BoujeeEnjinia1701/fieldcell/cad/drawings/FCL-DWG-002.pdf

CONCEPT, NOT FOR FABRICATION | FieldCell · github.com/BoujeeEnjinia1701/fieldcell

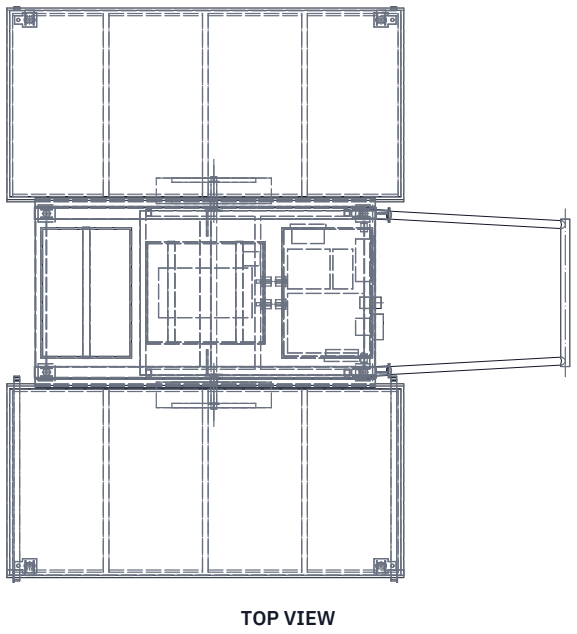
[picture p45: figure]
TOP VIEW

FRONT VIEW
Scale 1:25; looking at the front (along +Y)

Scale 1:25; looking down (along -Z)

RIGHT VIEW
Scale 1:25; looking at the right side (along -X)

1986

2030 916

460 deck

720 track

309

ISOMETRIC VIEW, STOWED FOR TRAVEL
Not to scale; seen from the front right and above, about 30 deg elevation

MAIN DIMENSIONS AND INTERFACES (MM)
Deployed 1,986 L x 2,030 W x 916 H; wingspan 2,012 Stowed, handle off: 1,400 x 830 x 1,220
Frame 1,200 x 600, 40 x 40 x 1.5 steel tube; deck 460 parked Wheels 406 dia., track 720; axle 30 toward handle
Hinge pin Y +/-330, Z 495; wings 15 deg below horizontal Hinge on 20 x 20 angle, welded tabs; wing to tyre 28
Sun shade on 4 uprights (item 18); tie bars (item 19)
Outlet face toward handle; grip at Z 900
Mass about 80.0 kg (FCL-CAL-001); 2 x 200 W PV, 1.28 kWh Third-angle; front view from -Y, right view from +X
REV | DESCRIPTION | DATE | BY
P1 | Preliminary GA for TRL 3 (from cad/src/model.py) | 2026-09-25 | AC
P2 | Hinge spacer +20 mm, sun shade added (DDR-002) | 2026-09-25 | AC
P3 | Layout and labels tidied | 2026-09-30 | AC
P4 | Constructable design (DDR-003): tabs, sockets, clevises, tie bars, shade uprights | 2026-10-01 | AC
FIELDCELL | github.com/BoujeeEnjinia1701/fieldcell

## General arrangement

DRAWING NO.
FCL-DWG-002

REV
P4

SHEET
1 of 1

SIZE

## ANSI B

SCALE
1:25

UNITS
mm
PROJECTION | DATE
2026-10-01

DRAWN
Amish Chadha

MATERIAL / NOTES
Welded steel frame, IP65 and IP54 enclosures; see bom/bom.csv. PRELIMINARY, NOT FOR FABRICATION
Licensed CERN-OHL-S-2.0 · Design Molecule Lab · designmolecule.com | Generated from cad/src; do not edit by hand
