BoujeeEnjinia1701/fieldcell/cad/drawings/FCL-DWG-101.pdf

### BUILD PLAN SKETCH, PLAN NOT YET BUILT FieldCell · github.com/BoujeeEnjinia1701/fieldcell

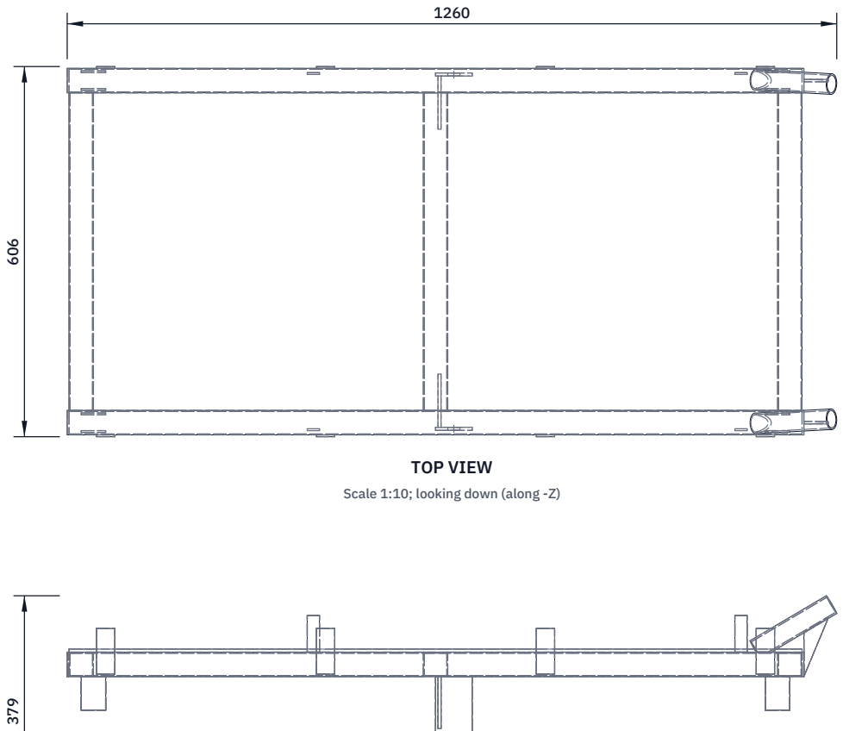
[picture p46: figure]
TOP VIEW; Scale 1:10; looking down (along -Z)
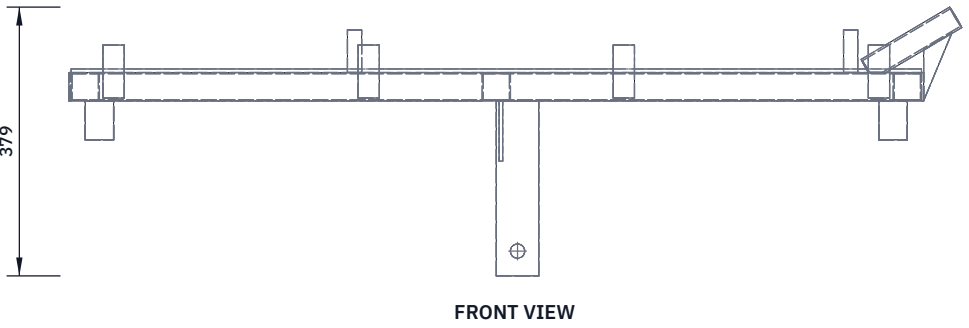
[picture p47: figure]
FRONT VIEW

Scale 1:10; looking at the front (along +Y)

RIGHT VIEW
Scale 1:10; looking at the right side (along -X)

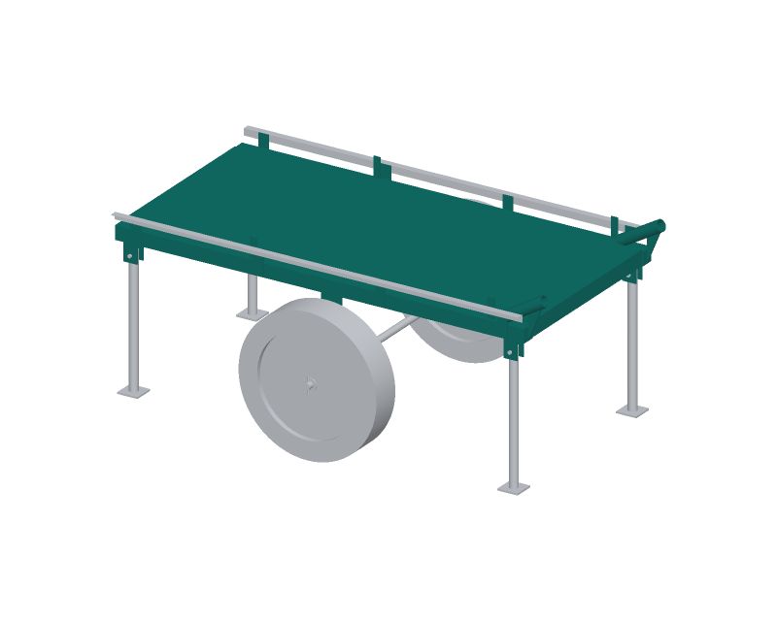
[picture p48: figure]

WHERE IT GOES
This part in colour, its neighbours in grey

HOW TO MAKE IT AND HOW IT FITS
Rails: two 1,200 mm lengths of 40 x 40 x 1.5 tube. Cross tubes: three
520 mm lengths, at both ends and the middle, between the rails.
Weld square on a flat table: diagonals equal within 2 mm. Tube tops
are 455 mm above the ground when parked. Cap the four rail ends (3 mm). Deck: expanded steel sheet 1,200 x 520 mm laid on the cross tubes between the rails, stitch welded 25 mm every 150 mm.
Axle brackets: 60 x 5 mm plate, 247 mm long, under each rail at 630 mm from the front end, 290 mm from the centre line; 20.5 mm axle hole
35 mm above the bottom. Gusset 87 x 85 x 5 mm to the middle cross tube. Hinge tabs: eight 30 x 3 mm, 75 mm long, on the rail outer faces at
60, 420, 780 and 1,140 mm from the front end, 39 mm above the rail top. Handle sockets, leg clevises, shade tabs: see the frame layout picture. Check: deck flat within 3 mm; axle holes line up (20 mm bar slides through).
REV | DESCRIPTION | DATE | BY
P1 | Making sketch for the prototype build plan | 2026-10-01 | AC
FIELDCELL | github.com/BoujeeEnjinia1701/fieldcell

## FieldCell frame weldment: making sketch

DRAWING NO.
FCL-DWG-101

REV
P1

SHEET
1 of 1

SIZE

## ANSI B

SCALE
1:10

UNITS
mm
PROJECTION | DATE
2026-10-01

DRAWN
Amish Chadha

MATERIAL / NOTES
Steel square tube 40 x 40 x 1.5, S235; expanded steel sheet; 3 to 5 mm plate
Licensed CERN-OHL-S-2.0 · Design Molecule Lab · designmolecule.com | Generated from cad/src; do not edit by hand
