BoujeeEnjinia1701/fieldcell/cad/drawings/FCL-DWG-102.pdf

### BUILD PLAN SKETCH, PLAN NOT YET BUILT FieldCell · github.com/BoujeeEnjinia1701/fieldcell

FRONT VIEW
Scale 1:5; looking at the front (along +Y)

TOP VIEW
Scale 1:5; looking down (along -Z)

RIGHT VIEW
Scale 1:5; looking at the right side (along -X)

820

20 20

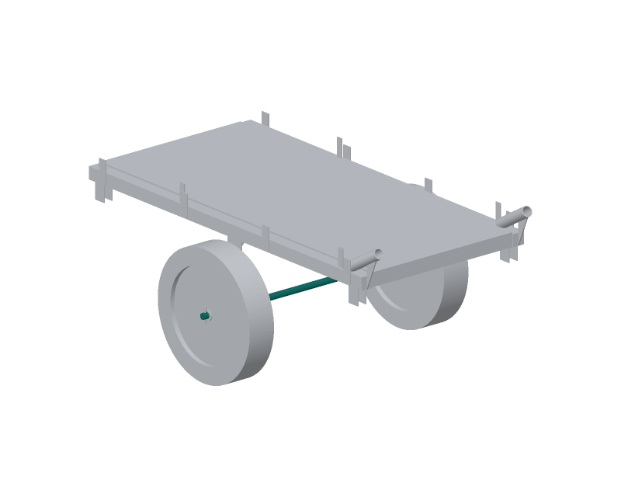
[picture p49: figure]

WHERE IT GOES
This part in colour, its neighbours in grey

HOW TO MAKE IT AND HOW IT FITS
Cut 820 mm of 20 mm bright steel bar; chamfer both ends 1 mm. Drill a 5 mm cross hole 10 mm from each end for the linch pins, both holes in the same plane.
Slide it through both bracket holes so 410 mm stands each side of the centre line; weld it to both brackets, all round, both faces. Each end then takes, in order: a spacer collar 26 mm outside,
20 mm bore, 37.5 mm long; the wheel hub (60 mm long);
a 20 mm washer 3 mm thick; the linch pin.
Check: the wheels spin freely with 0.5 to 1 mm end float.
REV | DESCRIPTION | DATE | BY
P1 | Making sketch for the prototype build plan | 2026-10-01 | AC
FIELDCELL | github.com/BoujeeEnjinia1701/fieldcell

## FieldCell axle: making sketch

DRAWING NO.
FCL-DWG-102

REV
P1

SHEET
1 of 1

SIZE

## ANSI B

SCALE
1:5

UNITS
mm
PROJECTION | DATE
2026-10-01

DRAWN
Amish Chadha

MATERIAL / NOTES
Bright mild steel bar 20 mm diameter
Licensed CERN-OHL-S-2.0 · Design Molecule Lab · designmolecule.com | Generated from cad/src; do not edit by hand
