BoujeeEnjinia1701/fieldcell/cad/drawings/FCL-DWG-103.pdf

### BUILD PLAN SKETCH, PLAN NOT YET BUILT FieldCell · github.com/BoujeeEnjinia1701/fieldcell

FRONT VIEW
Scale 1:5; looking at the front (along +Y)

TOP VIEW
Scale 1:5; looking down (along -Z)

RIGHT VIEW
Scale 1:5; looking at the right side (along -X)

60

60 392

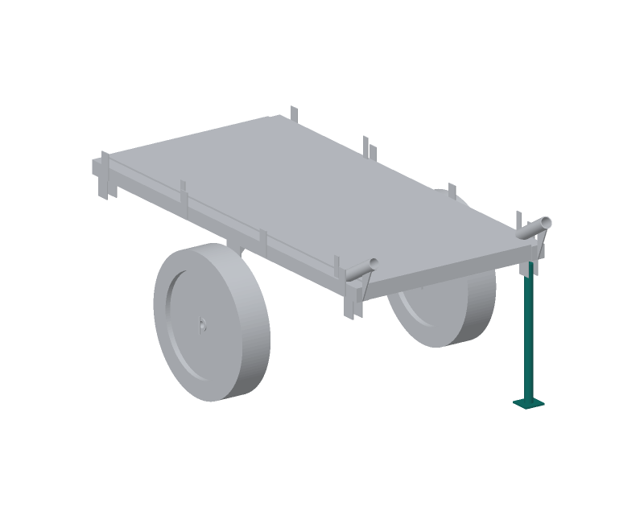
[picture p50: figure]

WHERE IT GOES
This part in colour, its neighbours in grey

HOW TO MAKE IT AND HOW IT FITS
Cut four 387 mm lengths of 25 x 2 mm tube; round the top end. Drill 10.5 mm across the tube 12 mm from the top: the pivot. Drill 6.5 mm across, 30 mm below the pivot hole: the detent hole that locks the leg down.
Weld a 60 x 60 x 5 mm foot plate square on the bottom end. Fit: the top end goes between a pair of 3 mm clevis plates under the rail, 40 mm from the rail end; M10 pivot bolt, nyloc nut, snug so the leg swings. Spring detent pin through the clevis and the leg holds it down; a second clevis hole holds it folded. The leg folds inward along the rail, foot toward the axle. Check: with all four down the deck is level within 1 degree.
REV | DESCRIPTION | DATE | BY
P1 | Making sketch for the prototype build plan | 2026-10-01 | AC
FIELDCELL | github.com/BoujeeEnjinia1701/fieldcell

## FieldCell stand leg (make 4): making sketch

DRAWING NO.
FCL-DWG-103

REV
P1

SHEET
1 of 1

SIZE

## ANSI B

SCALE
1:5

UNITS
mm
PROJECTION | DATE
2026-10-01

DRAWN
Amish Chadha

MATERIAL / NOTES
Steel tube 25 x 2 mm; steel plate 5 mm
Licensed CERN-OHL-S-2.0 · Design Molecule Lab · designmolecule.com | Generated from cad/src; do not edit by hand
