BoujeeEnjinia1701/fieldcell/cad/drawings/FCL-DWG-104.pdf

### BUILD PLAN SKETCH, PLAN NOT YET BUILT FieldCell · github.com/BoujeeEnjinia1701/fieldcell

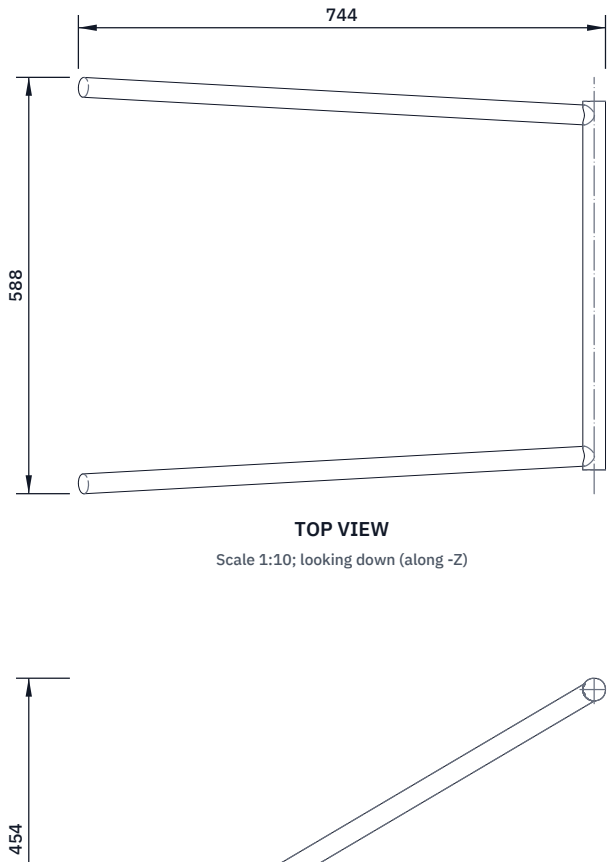
[picture p51: figure]
TOP VIEW; Scale 1:10; looking down (along -Z)

FRONT VIEW
Scale 1:10; looking at the front (along +Y)

RIGHT VIEW
Scale 1:10; looking at the right side (along -X)

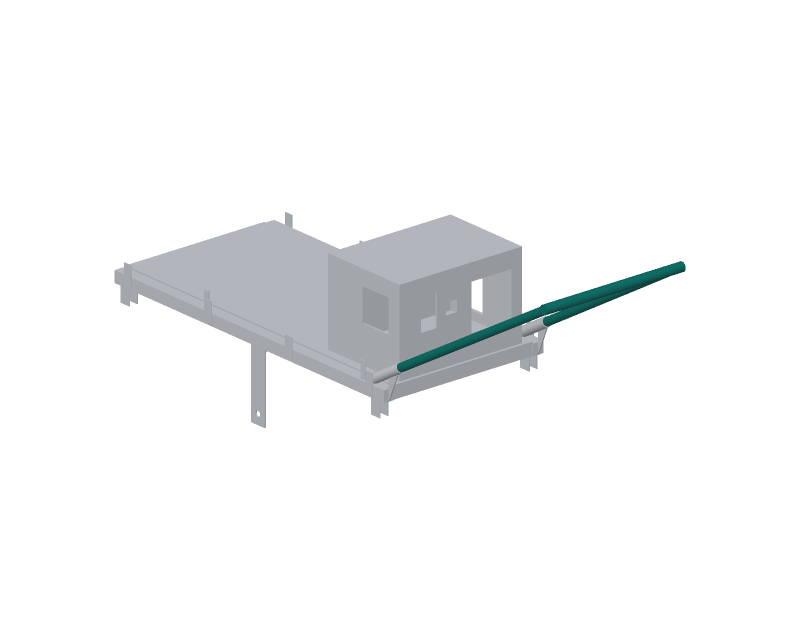
[picture p52: figure]

WHERE IT GOES
This part in colour, its neighbours in grey

HOW TO MAKE IT AND HOW IT FITS
Legs: two 843 mm lengths of 28 x 1.5 mm tube.
Grip: 520 mm of 32 x 1.5 mm tube.
Lay out on the bench: leg feet 560 mm apart, leg tops 480 mm apart, meeting the grip 20 mm in from each grip end. Fish-mouth the leg tops to the grip and weld.
Each leg drops into a socket on the rail end, 30.5 degrees up from level; mark the leg 115 mm from its foot and drill 8.5 mm across it with the leg in the socket, through the socket's pin hole. Quick-release pins hold the handle; pull them to take it off.
Grip 900 mm above the ground, 1,270 mm from the deck centre. Check: the handle drops in and out of both sockets without forcing.
REV | DESCRIPTION | DATE | BY
P1 | Making sketch for the prototype build plan | 2026-10-01 | AC
FIELDCELL | github.com/BoujeeEnjinia1701/fieldcell

## FieldCell handle: making sketch

DRAWING NO.
FCL-DWG-104

REV
P1

SHEET
1 of 1

SIZE

## ANSI B

SCALE
1:10

UNITS
mm
PROJECTION | DATE
2026-10-01

DRAWN
Amish Chadha

MATERIAL / NOTES
Steel tube 28 x 1.5 mm (legs), 32 x 1.5 mm (grip)
Licensed CERN-OHL-S-2.0 · Design Molecule Lab · designmolecule.com | Generated from cad/src; do not edit by hand
