BoujeeEnjinia1701/fieldcell/cad/drawings/FCL-DWG-105.pdf

### BUILD PLAN SKETCH, PLAN NOT YET BUILT FieldCell · github.com/BoujeeEnjinia1701/fieldcell

FRONT VIEW
Scale 1:10; looking at the front (along +Y)

TOP VIEW
Scale 1:10; looking down (along -Z)

RIGHT VIEW
Scale 1:10; looking at the right side (along -X)

1200

20 20

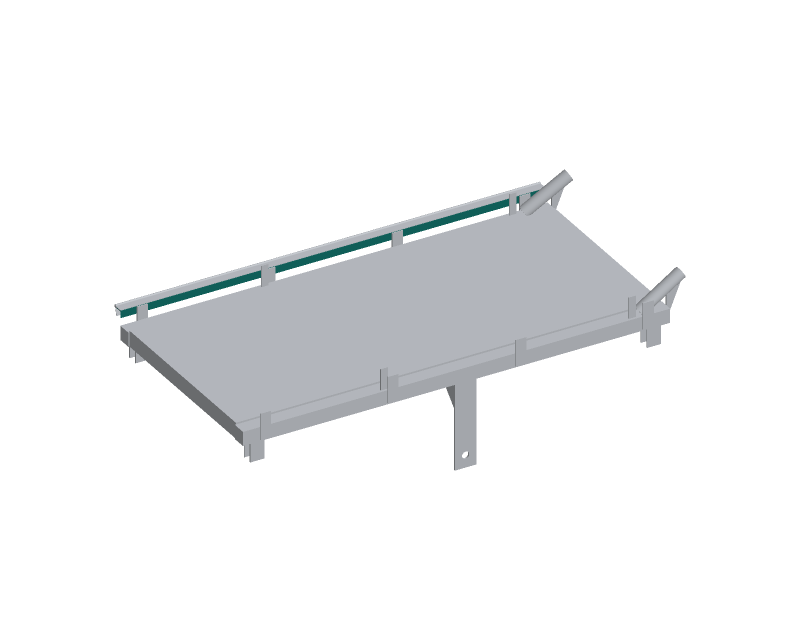
[picture p53: figure]

WHERE IT GOES
This part in colour, its neighbours in grey

HOW TO MAKE IT AND HOW IT FITS
Cut two 1,200 mm lengths of 20 x 20 x 2 mm angle; deburr. Upright leg: four 5.5 mm holes 11 mm down from the top, at 60, 420, 780 and 1,140 mm from one end, to match the frame tabs. Flat leg (top): 4.5 mm holes every 150 mm, 10 mm in from the outer edge, for the hinge screws; countersink from the top. Fit: upright leg flat on the outside of the four tabs, top of the flat leg 494 mm above the ground, flat leg pointing outward. M5 bolts through the tabs, nyloc nuts inside.
The hinge's fixed leaf lies on the flat leg; its knuckle (the pin) overhangs the angle's edge by 7 mm.
Check: angle top level and straight within 1 mm along its length.
REV | DESCRIPTION | DATE | BY
P1 | Making sketch for the prototype build plan | 2026-10-01 | AC
FIELDCELL | github.com/BoujeeEnjinia1701/fieldcell

## FieldCell hinge spacer angle (make 2): making sketch

DRAWING NO.
FCL-DWG-105

REV
P1

SHEET
1 of 1

SIZE

## ANSI B

SCALE
1:10

UNITS
mm
PROJECTION | DATE
2026-10-01

DRAWN
Amish Chadha

MATERIAL / NOTES
Aluminium equal angle 20 x 20 x 2 mm, 6063
Licensed CERN-OHL-S-2.0 · Design Molecule Lab · designmolecule.com | Generated from cad/src; do not edit by hand
