BoujeeEnjinia1701/fieldcell/cad/drawings/FCL-DWG-106.pdf

### BUILD PLAN SKETCH, PLAN NOT YET BUILT FieldCell · github.com/BoujeeEnjinia1701/fieldcell

FRONT VIEW
Scale 1:10; looking at the front (along +Y)

TOP VIEW
Scale 1:10; looking down (along -Z)

RIGHT VIEW
Scale 1:10; looking at the right side (along -X)

1400

700 30

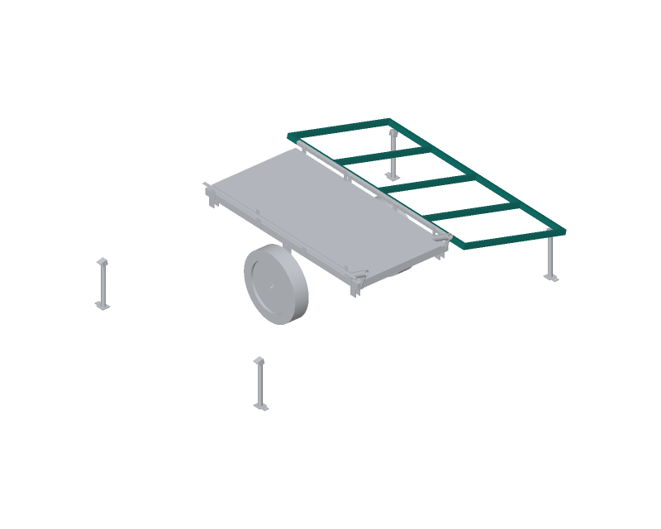
[picture p54: figure]

WHERE IT GOES
This part in colour, its neighbours in grey

HOW TO MAKE IT AND HOW IT FITS
Long members: two 1,400 mm lengths. End members and ribs: five
660 mm lengths. All 30 x 20 x 1.5 tube, 30 mm side upright.
Ribs at 350, 700 and 1,050 mm from one end, square to the long members. Join every butt with an aluminium corner cleat inside the tubes and
four 4.8 mm blind rivets (or TIG weld). Frame 1,400 x 700 mm.
Face (top): flat within 2 mm; the module is bonded to it.
Inner long member (hinge side): M4 rivet nuts every 150 mm in its inner face, 10 mm below the top, for the hinge's moving leaf.
Outer long member: outrigger brackets underneath at 80 mm from each end; tie bar bracket (left wing) or keeper (right wing) at each end. Check: diagonals equal within 2 mm; frame does not rock on a table.
REV | DESCRIPTION | DATE | BY
P1 | Making sketch for the prototype build plan | 2026-10-01 | AC
FIELDCELL | github.com/BoujeeEnjinia1701/fieldcell

## FieldCell PV wing frame (make 2): making sketch

DRAWING NO.
FCL-DWG-106

REV
P1

SHEET
1 of 1

SIZE

## ANSI B

SCALE
1:10

UNITS
mm
PROJECTION | DATE
2026-10-01

DRAWN
Amish Chadha

MATERIAL / NOTES
Aluminium rectangular tube 30 x 20 x 1.5 mm, 6063
Licensed CERN-OHL-S-2.0 · Design Molecule Lab · designmolecule.com | Generated from cad/src; do not edit by hand
