BoujeeEnjinia1701/fieldcell/cad/drawings/FCL-DWG-107.pdf

### BUILD PLAN SKETCH, PLAN NOT YET BUILT FieldCell · github.com/BoujeeEnjinia1701/fieldcell

FRONT VIEW
Scale 1:5; looking at the front (along +Y)

TOP VIEW
Scale 1:5; looking down (along -Z)

RIGHT VIEW
Scale 1:5; looking at the right side (along -X)

78

50 273

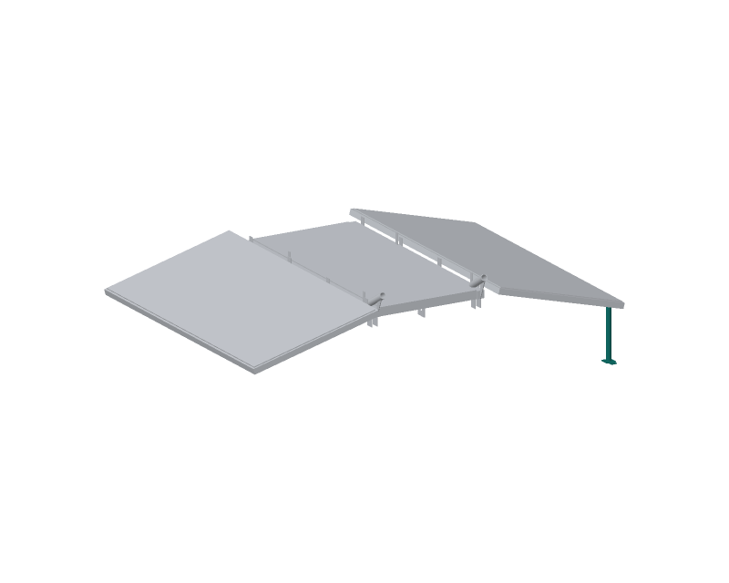
[picture p55: figure]

WHERE IT GOES
This part in colour, its neighbours in grey

HOW TO MAKE IT AND HOW IT FITS
Leg: cut 269 mm of 25 x 2 mm tube; round the top end; drill 8.5 mm across, 10 mm from the top (pivot), and 6.5 mm 30 mm below it (detent). Foot: 50 x 50 x 4 mm plate with a 28 x 30 mm stake tab on one side
(11 mm hole, 15 mm from the plate edge); weld square to the leg.
The tab points toward the nearer end of the cart.
Bracket: bend a 3 mm aluminium strip into a U, 26 mm inside, legs 29 mm, web 45 mm long; 8.5 mm pivot hole through both legs. Fit: rivet the web under the wing's outer long member, 80 mm from the frame end; M8 pivot bolt, nyloc nut, snug.
Leg down: vertical with the wing at 15 degrees. Folded: flat under the wing, 7 mm clear of the frame.
Check: the wing's outer edge sits 309 mm above the ground.
REV | DESCRIPTION | DATE | BY
P1 | Making sketch for the prototype build plan | 2026-10-01 | AC
FIELDCELL | github.com/BoujeeEnjinia1701/fieldcell

## FieldCell outrigger leg and bracket (make 4): making sketch

DRAWING NO.
FCL-DWG-107

REV
P1

SHEET
1 of 1

SIZE

## ANSI B

SCALE
1:5

UNITS
mm
PROJECTION | DATE
2026-10-01

DRAWN
Amish Chadha

MATERIAL / NOTES
Steel tube 25 x 2 mm, steel plate 4 mm; aluminium strip 3 mm (bracket)
Licensed CERN-OHL-S-2.0 · Design Molecule Lab · designmolecule.com | Generated from cad/src; do not edit by hand
