BoujeeEnjinia1701/fieldcell/cad/drawings/FCL-DWG-108.pdf

### BUILD PLAN SKETCH, PLAN NOT YET BUILT FieldCell · github.com/BoujeeEnjinia1701/fieldcell

FRONT VIEW
Scale 1:5; looking at the front (along +Y)

TOP VIEW
Scale 1:5; looking down (along -Z)

RIGHT VIEW
Scale 1:5; looking at the right side (along -X)

743

20 20

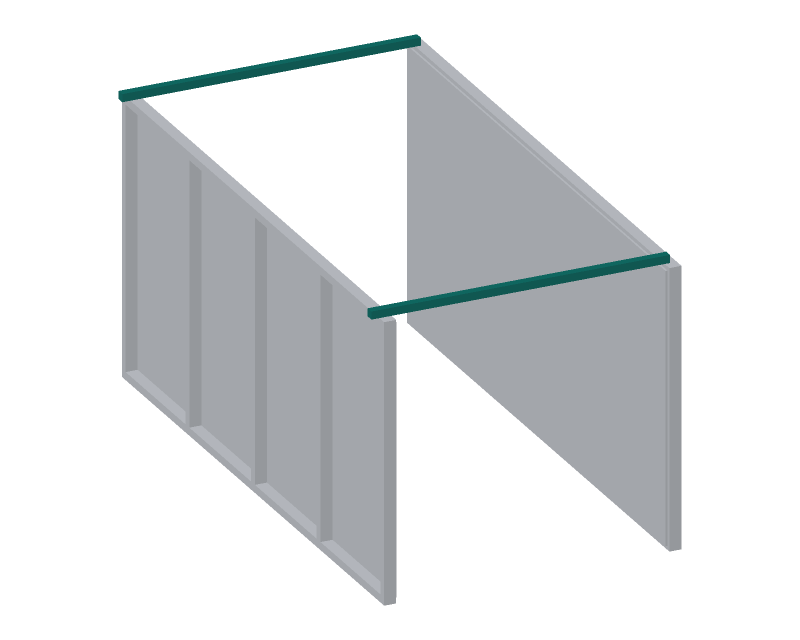
[picture p56: figure]

WHERE IT GOES
This part in colour, its neighbours in grey

HOW TO MAKE IT AND HOW IT FITS
Cut two 731 mm lengths of 20 x 20 x 1.5 mm square tube; deburr (743 mm overall with the latch body on the end).
Drill 6.5 mm across, 10 mm from one end: the pivot.
Rivet the over-centre latch body to the other end, hook outward. Pivot bracket: 3 mm aluminium angle, ear 35 mm tall beside the bar, riveted to the top corner of the left wing's frame, on its back. Keeper: screwed to the top of the right wing's outer member,
12 mm in from its back face, opposite the latch.
Travel: the bar lies across the tops of both stowed wings and the latch pulls the right wing in against it.
Parked: the bar folds down the back of the left wing, held by a clip. Check: latched, neither wing moves when pushed outward at the top.
REV | DESCRIPTION | DATE | BY
P1 | Making sketch for the prototype build plan | 2026-10-01 | AC
FIELDCELL | github.com/BoujeeEnjinia1701/fieldcell

## FieldCell tie bar (make 2): making sketch

DRAWING NO.
FCL-DWG-108

REV
P1

SHEET
1 of 1

SIZE

## ANSI B

SCALE
1:5

UNITS
mm
PROJECTION | DATE
2026-10-01

DRAWN
Amish Chadha

MATERIAL / NOTES
Aluminium square tube 20 x 20 x 1.5 mm, 6063
Licensed CERN-OHL-S-2.0 · Design Molecule Lab · designmolecule.com | Generated from cad/src; do not edit by hand
