BoujeeEnjinia1701/fieldcell/cad/drawings/FCL-DWG-109.pdf

### BUILD PLAN SKETCH, PLAN NOT YET BUILT FieldCell · github.com/BoujeeEnjinia1701/fieldcell

FRONT VIEW
Scale 1:10; looking at the front (along +Y)

TOP VIEW
Scale 1:10; looking down (along -Z)

RIGHT VIEW
Scale 1:10; looking at the right side (along -X)

830

580 375

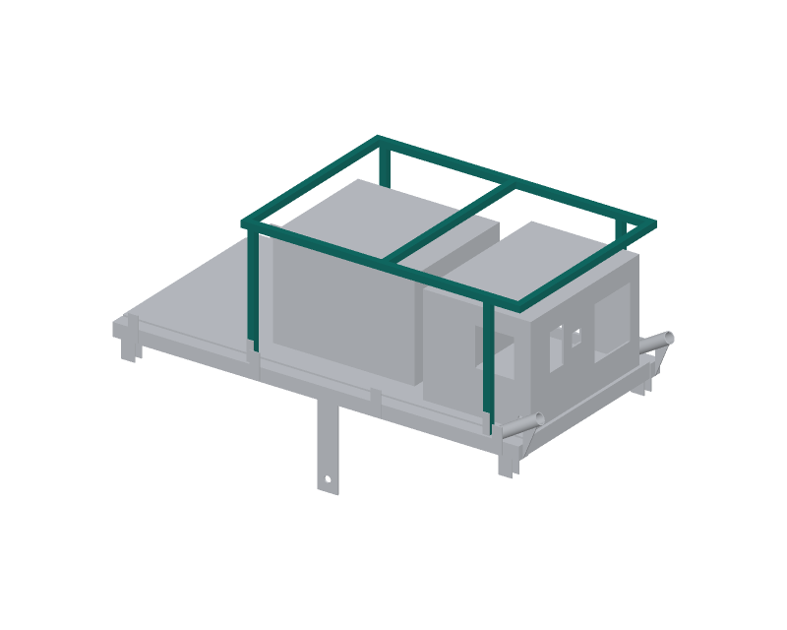
[picture p57: figure]

WHERE IT GOES
This part in colour, its neighbours in grey

HOW TO MAKE IT AND HOW IT FITS
Frame: two 830 mm long sides, three 540 mm cross tubes (ends and middle), 20 x 20 x 1.5 mm; corner cleats and rivets. 830 x 580 mm. Fabric: reflective aluminized fabric, 830 x 580 mm, eyelets every 100 mm, laced round the frame, shiny side up.
Uprights: four 355 mm lengths of the same tube. 6.5 mm hole across each, 30 mm from the bottom, for the M6 bolt into the frame tab. Uprights stand on the rail tops at 400 and 1,100 mm from the front end, 280 mm each side of the centre line.
The frame's long sides rest on the upright tops 810 mm above the ground, 50 mm over both boxes; an angle clip and M6 wing bolt at each upright. Undo four wing bolts to lift the shade off and open the battery lid.
Check: 50 mm air gap over both boxes; shade level within 5 mm.
REV | DESCRIPTION | DATE | BY
P1 | Making sketch for the prototype build plan | 2026-10-01 | AC
FIELDCELL | github.com/BoujeeEnjinia1701/fieldcell

## FieldCell sun shade frame and uprights: making sketch

DRAWING NO.
FCL-DWG-109

REV
P1

SHEET
1 of 1

SIZE

## ANSI B

SCALE
1:10

UNITS
mm
PROJECTION | DATE
2026-10-01

DRAWN
Amish Chadha

MATERIAL / NOTES
Aluminium square tube 20 x 20 x 1.5 mm; aluminized fabric
Licensed CERN-OHL-S-2.0 · Design Molecule Lab · designmolecule.com | Generated from cad/src; do not edit by hand
