BoujeeEnjinia1701/fieldcell/cad/drawings/FCL-DWG-110.pdf

### BUILD PLAN SKETCH, PLAN NOT YET BUILT FieldCell · github.com/BoujeeEnjinia1701/fieldcell

FRONT VIEW
Scale 1:10; looking at the front (along +Y)

TOP VIEW
Scale 1:10; looking down (along -Z)

RIGHT VIEW
Scale 1:10; looking at the right side (along -X)

320

460 260

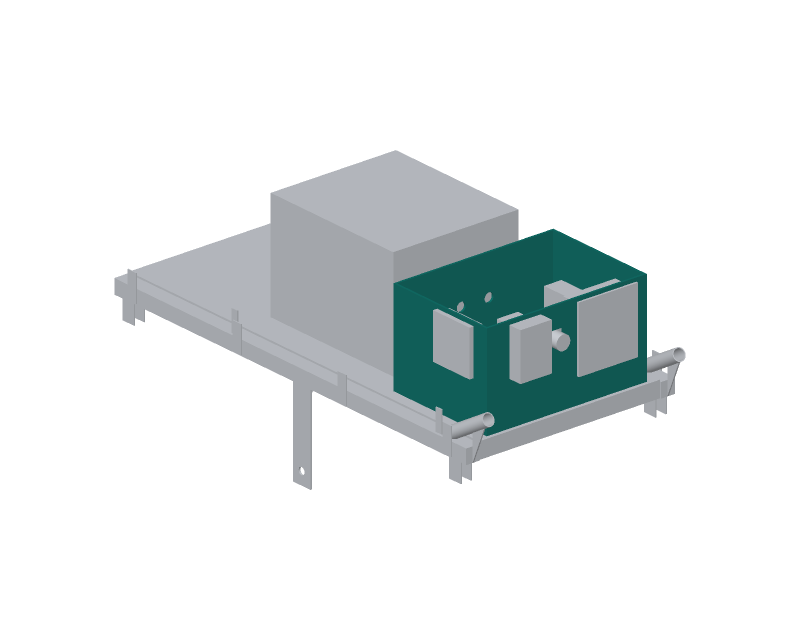
[picture p58: figure]

WHERE IT GOES
This part in colour, its neighbours in grey

HOW TO MAKE IT AND HOW IT FITS
Sizes are from the box's outside bottom edge and its centre line. Outlet end (toward the handle): DC panel 150 x 160 mm, 40 to 190 mm right of centre, 80 to 240 mm up; AC outlet 60 x 110 mm, 90 to 150 mm left, 130 to 240 mm up; isolator 40 x 40 mm, 15 to 55 mm left, 160 to 200 mm up. (Right and left as seen facing that end.)
Right side wall: fan 115 x 115 mm, 35 to 150 mm from the battery end, 35 to 150 mm up. Left wall: exhaust 115 x 115 mm, 155 to 270 mm from the battery end, 130 to 245 mm up.
Battery end: two 25.5 mm gland holes, 40 mm each side, 150 mm up. Both side walls: a 16.5 mm PV gland hole 30 mm from the outlet end, 30 mm up. Floor: four 6.5 mm holes for the deck bolts.
Cut with a step drill and a fine jigsaw; tape first; no solvents.
REV | DESCRIPTION | DATE | BY
P1 | Making sketch for the prototype build plan | 2026-10-01 | AC
FIELDCELL | github.com/BoujeeEnjinia1701/fieldcell

## FieldCell electronics box: cutting sketch

DRAWING NO.
FCL-DWG-110

REV
P1

SHEET
1 of 1

SIZE

## ANSI B

SCALE
1:10

UNITS
mm
PROJECTION | DATE
2026-10-01

DRAWN
Amish Chadha

MATERIAL / NOTES
Bought IP54 polycarbonate box 320 x 460 x 300 mm
Licensed CERN-OHL-S-2.0 · Design Molecule Lab · designmolecule.com | Generated from cad/src; do not edit by hand
