BoujeeEnjinia1701/fieldcell/cad/drawings/FCL-DWG-111.pdf

### BUILD PLAN SKETCH, PLAN NOT YET BUILT FieldCell · github.com/BoujeeEnjinia1701/fieldcell

FRONT VIEW
Scale 1:5; looking at the front (along +Y)

TOP VIEW
Scale 1:5; looking down (along -Z)

RIGHT VIEW
Scale 1:5; looking at the right side (along -X)

420

360 260

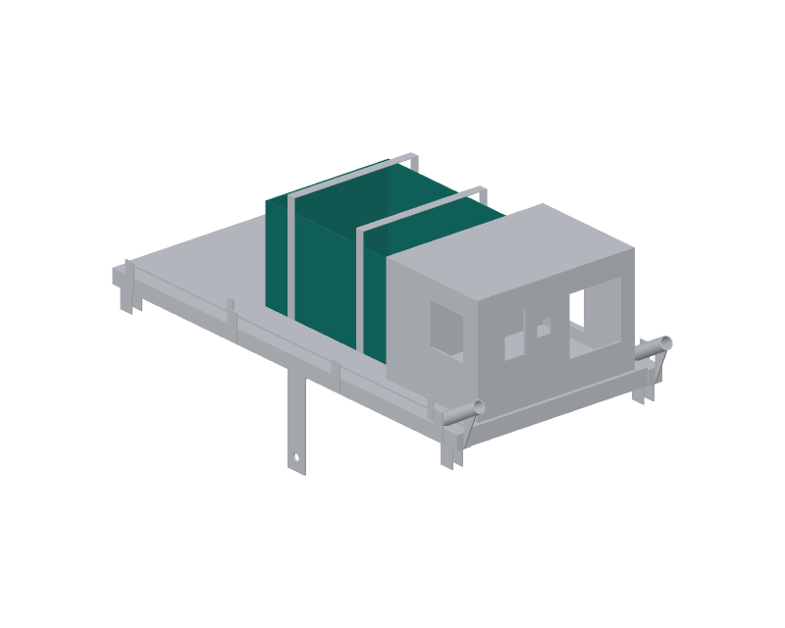
[picture p59: figure]

WHERE IT GOES
This part in colour, its neighbours in grey

HOW TO MAKE IT AND HOW IT FITS
Only the end facing the electronics box is drilled.
Two 25.5 mm holes for M25 glands, 40 mm each side of the centre line, 150 mm up from the outside bottom: they line up with the gland holes in the electronics box, 60 mm away.
Tape, pilot 3 mm, open with a step drill; deburr; no solvents.
Keep the case's own pressure vent; do not block it.
Inside: the pack sits in the middle of the floor on a 3 mm rubber mat with foam blocks round it; the class T fuse holder is screwed to
the floor beside the pack at the gland end, so the positive lead
from the pack to the fuse is under 150 mm.
Two cam straps hold the case and lid down through the deck. Check: glands seat flat; lid closes on its seal with the cables in.
REV | DESCRIPTION | DATE | BY
P1 | Making sketch for the prototype build plan | 2026-10-01 | AC
FIELDCELL | github.com/BoujeeEnjinia1701/fieldcell

## FieldCell battery case: drilling sketch

DRAWING NO.
FCL-DWG-111

REV
P1

SHEET
1 of 1

SIZE

## ANSI B

SCALE
1:5

UNITS
mm
PROJECTION | DATE
2026-10-01

DRAWN
Amish Chadha

MATERIAL / NOTES
Bought IP65 polypropylene case about 420 x 360 x 300 mm
Licensed CERN-OHL-S-2.0 · Design Molecule Lab · designmolecule.com | Generated from cad/src; do not edit by hand
