BoujeeEnjinia1701/fieldcell/cad/drawings/FCL-DWG-002.png

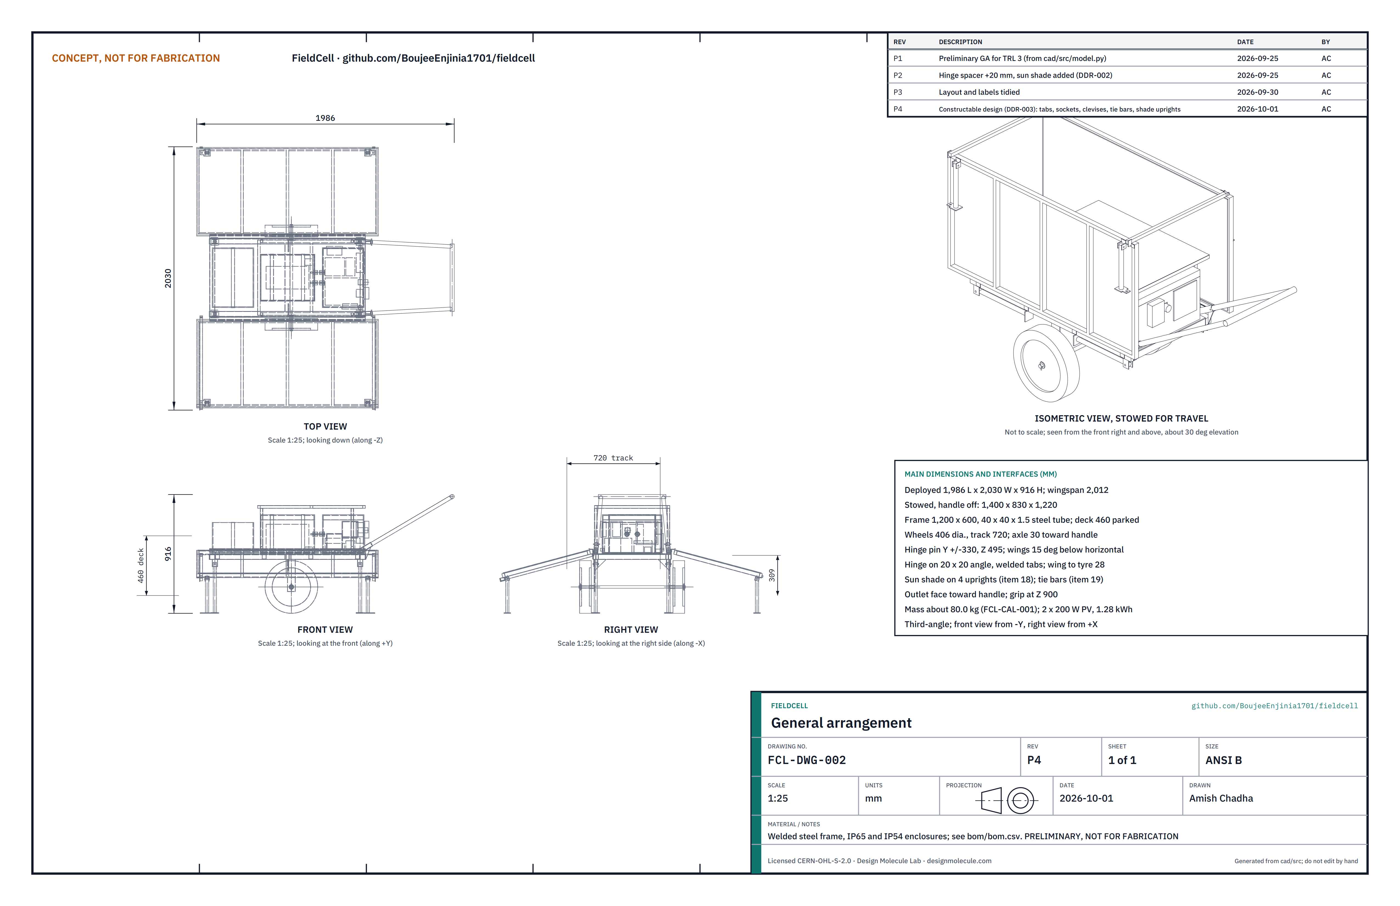
cad/drawings/FCL-DWG-002.png
