BoujeeEnjinia1701/fieldcell/media/card.png

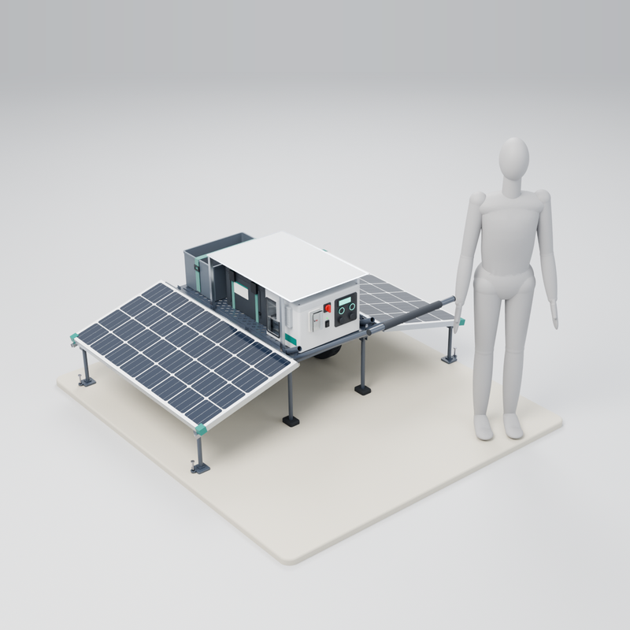
media/card.png
