BoujeeEnjinia1701/fieldcell/media/concept-blueprint.png

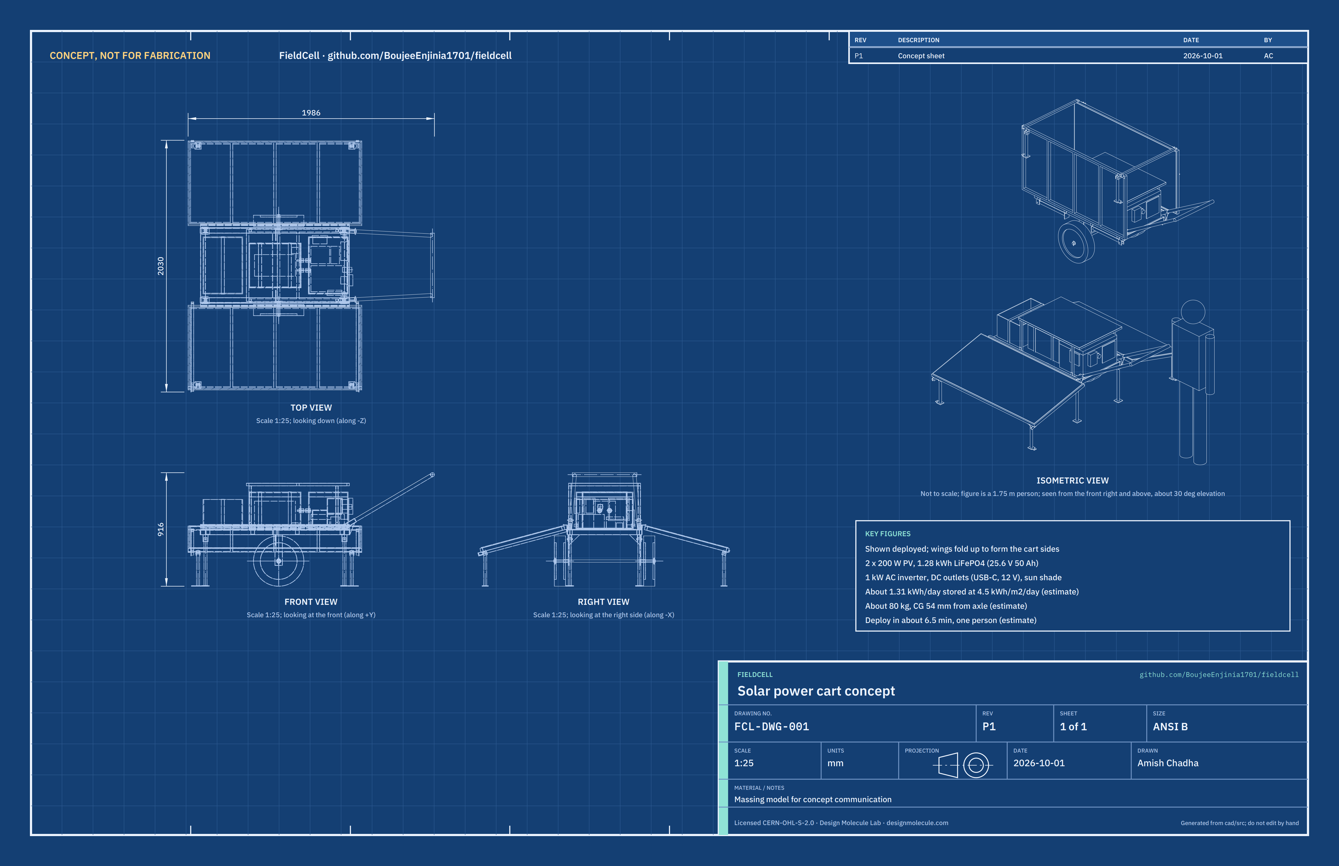
media/concept-blueprint.png
