BoujeeEnjinia1701/fieldcell/media/cutaway.png

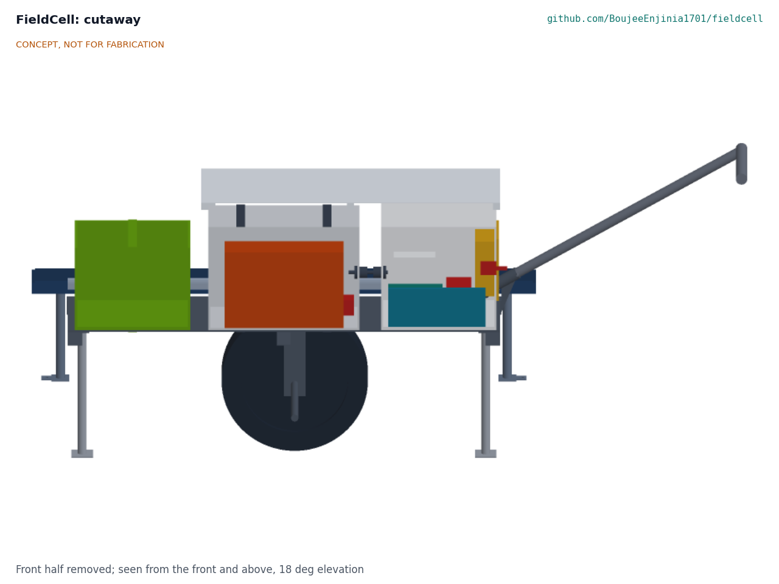
media/cutaway.png
