BoujeeEnjinia1701/fieldcell/media/render-detail.png

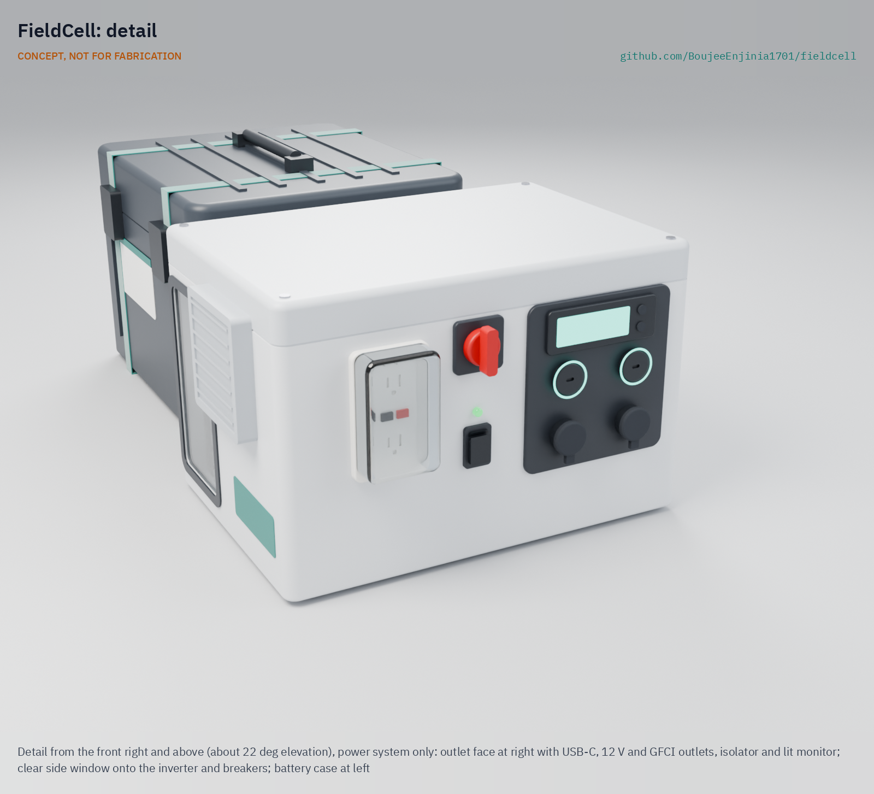
media/render-detail.png
