BoujeeEnjinia1701/fieldcell/media/render-exploded.png

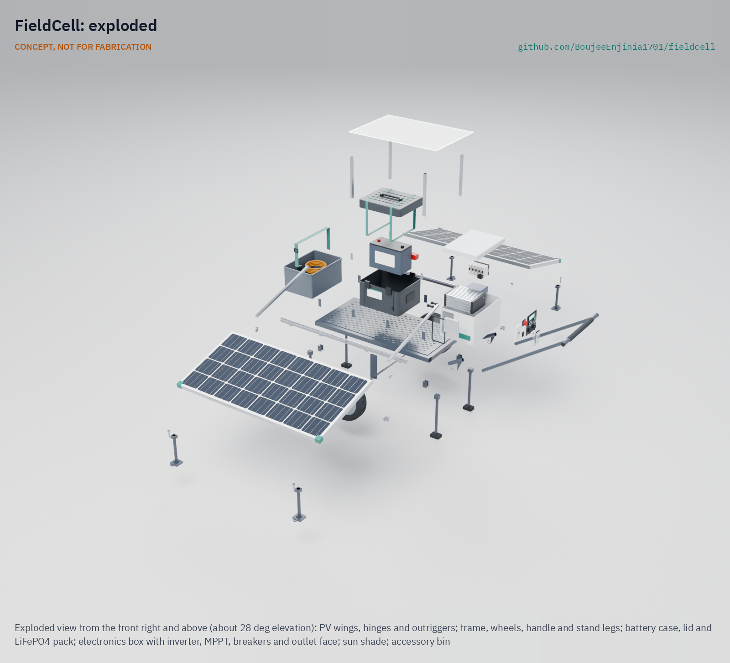
media/render-exploded.png
