BoujeeEnjinia1701/fieldcell/media/social-preview.png

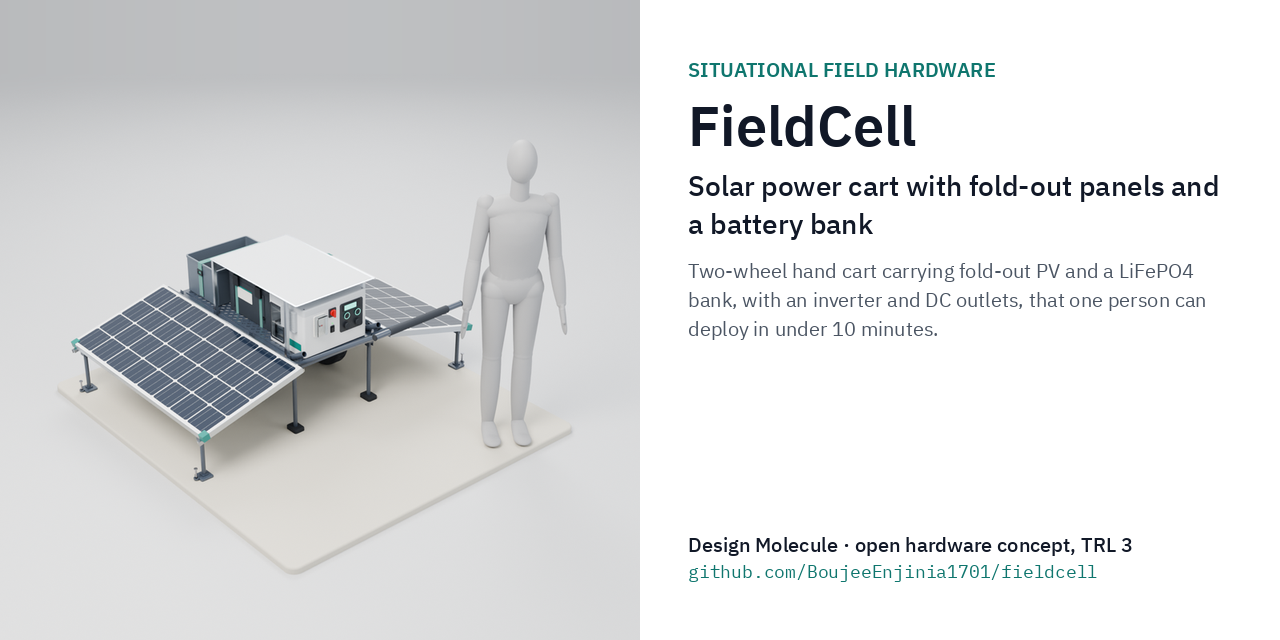
media/social-preview.png
